aidanmontag13/MultiPlaneDisplay/3Dmodels/tex_u0_v0_diffuse.jpg

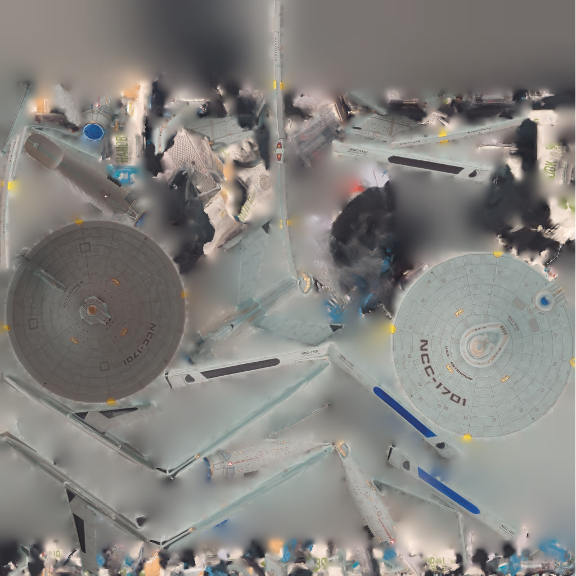
3Dmodels/tex_u0_v0_diffuse.jpg
