aidanmontag13/MultiPlaneDisplay/6.jpg

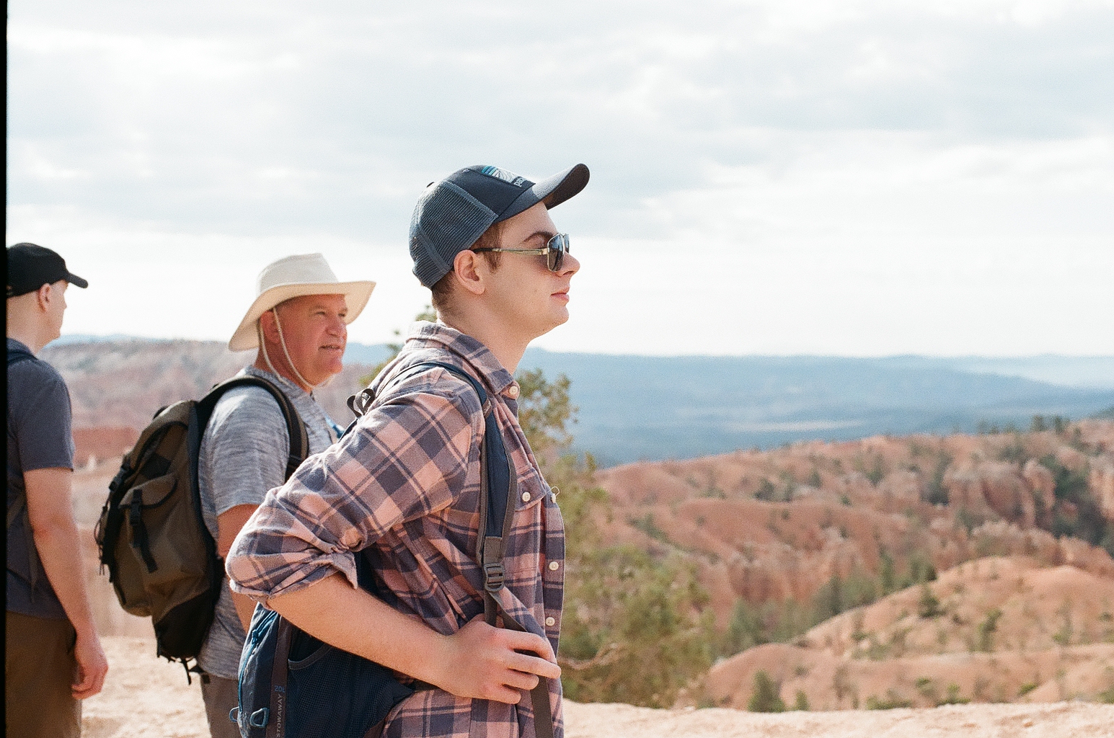
6.jpg
