aidanmontag13/MultiPlaneDisplay/artifacts/Diagram2.png

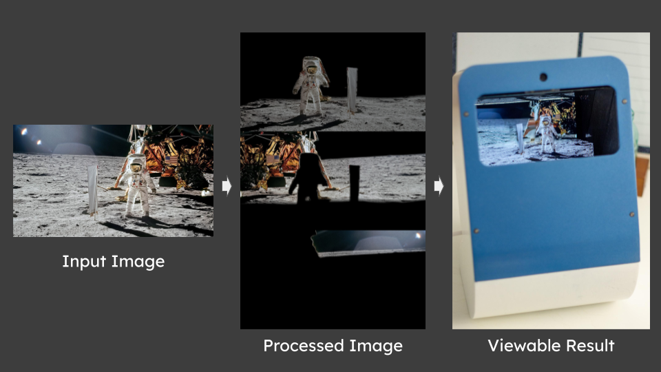
artifacts/Diagram2.png
