aidanmontag13/MultiPlaneDisplay/artifacts/Render.png

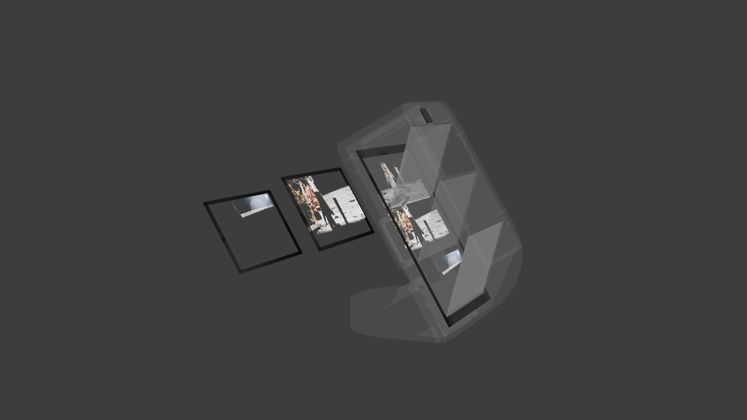
artifacts/Render.png
