aidanmontag13/MultiPlaneDisplay/multiplane_headtracker.py

from math import sqrt
import onnxruntime as ort
import cv2
import numpy as np
import glob
import os
import time
import copy
import open3d as o3d
from skimage.filters import threshold_multiotsu

import headtracker
import queue
import threading
from ultralytics import YOLO

H = 213
W = 400
PROJECTION_DISTANCE = 0.3
SCREEN_0_DISTANCE = 0.0
SCREEN_1_DISTANCE = 0.07239
SCREEN_2_DISTANCE = 0.1452
DEPTH_RANGE = 0.21718
DISPLAY_WIDTH = 0.13596

# Load model
session = ort.InferenceSession(
    "models/depth_anything/depth_anything_v2_vits.onnx",
    providers=['CPUExecutionProvider']
)

# Get correct input name
input_name = session.get_inputs()[0].name

def find_usb_images():
    user = "multiplane"
    media_root = f"/media/{user}"

    image_paths = []

    # Loop over all USB drives
    for drive in os.listdir(media_root):
        drive_path = os.path.join(media_root, drive)
        images_folder = os.path.join(drive_path, "images")
        output_folder = os.path.join(drive_path, "display")

        if os.path.isdir(images_folder):
            print(f"Found images folder on USB: {images_folder}")

            # Add all image files (jpg, png, tiff)
            for ext in ("*.jpg", "*.jpeg", "*.png", "*.tif", "*.tiff"):
                image_paths.extend(glob.glob(os.path.join(images_folder, ext)))
        else:
            print(f"No images folder found on USB: {drive_path}")
            continue

    return image_paths, output_folder

def resize_and_crop(img, target_size):
    target_w, target_h = target_size
    h, w = img.shape[:2]
    
    # Compute scale factor to cover the target
    scale = target_w / w
    
    # Resize image
    new_w = int(w * scale)
    new_h = int(h * scale)
    #print(f"Resizing from ({w}, {h}) to ({new_w}, {new_h})")
    if w / h > target_w / target_h:
        resized = cv2.resize(img, (new_w, target_h), interpolation=cv2.INTER_LINEAR)
        start_x = (new_w - target_w) // 2
        cropped = resized[:, start_x:start_x + target_w]
    else:
        resized = cv2.resize(img, (target_w, new_h), interpolation=cv2.INTER_LINEAR)
        start_y = (new_h - target_h) // 2
        cropped = resized[start_y:start_y + target_h, :]
    
    return cropped

def preprocess(image):
    img = cv2.cvtColor(image, cv2.COLOR_BGR2RGB)
    img = cv2.resize(img, (518, 518))
    img = img.astype(np.float32) / 255.0

    # model normalization
    mean = np.array([0.5, 0.5, 0.5], dtype=np.float32)
    std  = np.array([0.5, 0.5, 0.5], dtype=np.float32)
    img = (img - mean) / std

    img = img.transpose(2, 0, 1)  # HWC → CHW
    img = img[None, ...]          # add batch dim
    return img

def infer(inp):
    out = session.run(None, {input_name: inp})
    depth = out[0][0]

    # rescale depth for saving
    depth = (depth - depth.min()) / (depth.max() - depth.min())
    return depth

def create_pointcloud(color, depth):

    depth = depth * DEPTH_RANGE + (PROJECTION_DISTANCE - DEPTH_RANGE / 6)

    h, w = color.shape[:2]
    depth = cv2.resize(depth, (w, h), interpolation=cv2.INTER_LINEAR)

    fx = (w / DISPLAY_WIDTH) * PROJECTION_DISTANCE
    fy = fx
    cx = W / 2
    cy = H / 2

    color_o3d = o3d.geometry.Image((color).astype(np.uint8))
    depth_o3d = o3d.geometry.Image((depth * (1000)).astype(np.uint16))

    rgbd_image = o3d.geometry.RGBDImage.create_from_color_and_depth(
        color_o3d, depth_o3d, convert_rgb_to_intensity=False
    )

    intrinsics = o3d.camera.PinholeCameraIntrinsic(w, h, fx, fy, cx, cy)
    pcd = o3d.geometry.PointCloud.create_from_rgbd_image(rgbd_image, intrinsics)
    pcd, ind = pcd.remove_statistical_outlier(nb_neighbors=20, std_ratio=2.0)

    origin = o3d.geometry.TriangleMesh.create_coordinate_frame(size=0.01)

    o3d.visualization.draw_geometries([pcd, origin])

    return pcd

def despeckle(mask, kernel_size):
    kernel = np.ones((kernel_size,kernel_size), np.uint8)   # or (5,5) depending on outline thickness
    mask = mask * -1 + 1
    mask = (mask * 255).astype(np.uint8)
    closed = cv2.morphologyEx(mask, cv2.MORPH_CLOSE, kernel)
    mask = (closed.astype(np.float32)) / 255.0
    mask = mask * -1 + 1
    return mask

def blur_and_dilate(mask, blur_size):
    mask = mask * -1 + 1
    kernel = np.ones((int(blur_size * 0.3), int(blur_size * 0.3)), np.uint8)
    mask_uint8 = (mask * 255).astype(np.uint8)
    expanded = cv2.dilate(mask_uint8, kernel)
    mask = expanded.astype(np.float32) / 255.0
    mask = mask * -1 + 1
    mask = cv2.GaussianBlur(mask, (blur_size, blur_size), 0)
    return mask

def create_mask(depth, low_thresh, high_thresh, rolloff_a, rolloff_b, blur):
    mask = np.zeros_like(depth, dtype=np.float32)

    if rolloff_a == 0 and rolloff_b == 0:
        mask = ((depth >= low_thresh) & (depth <= high_thresh)).astype(np.float32)
        mask = blur_and_dilate(mask, blur)
        mask = despeckle(mask, kernel_size=3)
        mask = cv2.resize(mask, (W, H), interpolation=cv2.INTER_LINEAR)
        return mask
    
    lower_ramp = (depth - (low_thresh - 0.5 * rolloff_a)) / rolloff_a
    lower_ramp = np.clip(lower_ramp, 0, 1)
    
    upper_ramp = ((high_thresh + 0.5 * rolloff_b) - depth) / rolloff_b
    upper_ramp = np.clip(upper_ramp, 0, 1)
    
    if low_thresh == 0:
        mask = upper_ramp
    elif high_thresh == 1:
        mask = lower_ramp
    else:
        mask = np.minimum(lower_ramp, upper_ramp)

    mask = despeckle(mask, kernel_size=3)
    mask = blur_and_dilate(mask, blur)

    mask = cv2.resize(mask, (W, H), interpolation=cv2.INTER_LINEAR)
    
    return mask

def apply_mask(image, mask):
    mask = np.repeat(mask[:, :, np.newaxis], 3, axis=2)
    masked_image = image * mask
    return masked_image

def inpaint_mask(image, mask):
    mask = 1.0 - mask
    mask = cv2.resize(mask, (W, H), interpolation=cv2.INTER_LINEAR)
    mask_uint8 = (mask * 255).astype(np.uint8)
    kernel = np.ones((int(3), int(3)), np.uint8)
    mask = cv2.dilate(mask_uint8, kernel)
    inpainted = cv2.inpaint((image * 255).astype(np.uint8), mask_uint8, 5, cv2.INPAINT_NS)
    inpainted = inpainted.astype(np.float32) / 255.0
    return inpainted

def render_perspective(point_cloud, viewer_position, inpaint=True):
    pcd = copy.deepcopy(point_cloud)
    fx = (W / DISPLAY_WIDTH) * PROJECTION_DISTANCE
    fy = fx
    cx = W / 2
    cy = H / 2

    # move point cloud to center
    translation = np.array([0, 0, -PROJECTION_DISTANCE])
    pcd.translate(translation, relative=True)

    # calculate pitch and yaw angle to keep camera centered
    yaw_angle = np.arctan((viewer_position[0]) / viewer_position[1])
    pitch_angle = np.arctan((viewer_position[2]) / viewer_position[1])

    # rotate object
    rotation_matrix = pcd.get_rotation_matrix_from_xyz((pitch_angle, yaw_angle, 0))
    pcd.rotate(rotation_matrix, center=(0, 0, 0))

    # find offset
    viewer_distance = np.linalg.norm(viewer_position)
    offset_translation = np.array([0, 0, viewer_distance])
    pcd.translate(offset_translation, relative=True)

    #origin = o3d.geometry.TriangleMesh.create_coordinate_frame(size=0.1)

    #o3d.visualization.draw_geometries([pcd, pcd_og, origin])

    # Project point cloud back to image plane
    points = np.asarray(pcd.points)
    colors = np.asarray(pcd.colors)
    
    # Project 3D points to 2D
    x_proj = (points[:, 0] * fx / points[:, 2]) + cx
    y_proj = (points[:, 1] * fy / points[:, 2]) + cy
    
    # Create output image and depth buffer
    warped = np.zeros((H, W, 3), dtype=np.float32)
    depth_buffer = np.full((H, W), np.inf, dtype=np.float32)
    
    # Render points to image, keeping closest point
    valid_mask = (points[:, 2] > 0) & \
                 (x_proj >= 0) & (x_proj < W) & \
                 (y_proj >= 0) & (y_proj < H)
    
    x_proj = x_proj[valid_mask].astype(np.int32)
    y_proj = y_proj[valid_mask].astype(np.int32)
    z_depth = points[valid_mask, 2]
    colors_valid = colors[valid_mask]
    
    for i in range(len(x_proj)):
        # Only update if this point is closer than what's already there
        if z_depth[i] < depth_buffer[y_proj[i], x_proj[i]]:
            warped[y_proj[i], x_proj[i]] = colors_valid[i]
            depth_buffer[y_proj[i], x_proj[i]] = z_depth[i]

    mask = (depth_buffer == np.inf).astype(np.uint8)
    mask = 1 - mask
    
    if inpaint == True:
        warped = inpaint_mask(warped, mask)
        depth_buffer = inpaint_mask(depth_buffer, mask)
    
    return warped, depth_buffer, viewer_distance

def legacy_render_perspective(point_cloud, viewer_position, inpaint=True):
    
    pcd = copy.deepcopy(point_cloud)
    fx = (W / DISPLAY_WIDTH) * PROJECTION_DISTANCE
    fy = fx
    cx = W / 2
    cy = H / 2

    # move point cloud to center
    translation = np.array([0, 0, -PROJECTION_DISTANCE])
    pcd.translate(translation, relative=True)

    # calculate pitch and yaw angle to keep camera centered
    yaw_angle = np.arctan((viewer_position[0]) / viewer_position[1])
    pitch_angle = np.arctan((viewer_position[2]) / viewer_position[1])

    # rotate object
    rotation_matrix = pcd.get_rotation_matrix_from_xyz((pitch_angle, yaw_angle, 0))
    pcd.rotate(rotation_matrix, center=(0, 0, 0))

    # find offset
    viewer_distance = np.linalg.norm(viewer_position)
    offset_translation = np.array([0, 0, viewer_distance])
    pcd.translate(offset_translation, relative=True)

    vis = o3d.visualization.Visualizer()
    vis.create_window(visible=False, width=W, height=H)

    w_act = vis.get_render_option().mesh_show_back_face  # fake call just to init controller
    ctr = vis.get_view_control()

    params_now = ctr.convert_to_pinhole_camera_parameters()
    print("Window intrinsic size actually used by Open3D:", 
      params_now.intrinsic.width, params_now.intrinsic.height)

    vis.add_geometry(pcd)

    intrinsic = o3d.camera.PinholeCameraIntrinsic()
    intrinsic.set_intrinsics(W, H, fx, fy, cx, cy)

    extrinsic = np.eye(4) 

    cam_params = o3d.camera.PinholeCameraParameters()
    cam_params.intrinsic = intrinsic
    print("intrinsic", cam_params.intrinsic)
    cam_params.extrinsic = extrinsic

    ctr = vis.get_view_control()
    ctr.convert_from_pinhole_camera_parameters(cam_params)

    vis.poll_events()
    vis.update_renderer()

    color_o3d = vis.capture_screen_float_buffer(do_render=True)
    depth_o3d = vis.capture_depth_float_buffer(do_render=True)

    vis.destroy_window()

    color = np.asarray(color_o3d, dtype=np.float32)
    depth = np.asarray(depth_o3d, dtype=np.float32)

    if inpaint:
        mask = (depth > 0).astype(np.uint8)
        color = inpaint_mask(color, mask)
        depth = inpaint_mask(depth, mask)

    return color, depth, viewer_distance

def new_render_perspective(point_cloud, viewer_position, inpaint=True):
    pcd = copy.deepcopy(point_cloud)

    fx = (W / DISPLAY_WIDTH) * PROJECTION_DISTANCE
    fy = fx
    cx = W / 2
    cy = H / 2

    # move point cloud to center
    translation = np.array([0, 0, -PROJECTION_DISTANCE])
    pcd.translate(translation, relative=True)

    # your yaw/pitch system
    yaw_angle   = np.arctan((viewer_position[0]) / viewer_position[1])
    pitch_angle = np.arctan((viewer_position[2]) / viewer_position[1])

    rotation_matrix = pcd.get_rotation_matrix_from_xyz((pitch_angle, yaw_angle, 0))
    pcd.rotate(rotation_matrix, center=(0, 0, 0))

    # your offset
    viewer_distance = np.linalg.norm(viewer_position)
    offset_translation = np.array([0, 0, viewer_distance])
    pcd.translate(offset_translation, relative=True)

    renderer = o3d.visualization.rendering.OffscreenRenderer(W, H)
    scene = renderer.scene
    scene.set_background([0, 0, 0, 0])

    # add geometry
    material = o3d.visualization.rendering.MaterialRecord()
    material.shader = "defaultUnlit"
    material.point_size = 2.0
    scene.add_geometry("pcd", pcd, material)

    K = np.array([
        [fx, 0,  cx],
        [0,  fy, cy],
        [0,  0,   1]
    ], dtype=np.float64)

    # extrinsic is identity, because you ALREADY moved + rotated the point cloud
    extrinsic = np.eye(4)

    renderer.setup_camera(
        intrinsic_matrix=K,
        extrinsic_matrix=extrinsic,
        intrinsic_width_px=W,
        intrinsic_height_px=H
    )

    color_o3d = renderer.render_to_image()
    depth_o3d = renderer.render_to_depth_image(z_in_view_space=True)

    color = (np.asarray(color_o3d).astype(np.float32) / 255.0)
    depth = np.asarray(depth_o3d).astype(np.float32)

    if inpaint:
        mask = (depth > 0).astype(np.uint8)
        color = inpaint_mask(color, mask)
        depth = inpaint_mask(depth, mask)

    return color, depth

def reproject_2D(color, viewer_position, plane_depth):
    h, w = color.shape[:2]
    fx = (w / DISPLAY_WIDTH) * PROJECTION_DISTANCE
    fy = fx
    cx = W / 2
    cy = H / 2
    
    K = np.array([
        [fx, 0, cx],
        [0, fy, cy],
        [0, 0, 1]
    ])
    
    src_points = np.float32([
        [0, 0],           # Top-left
        [W, 0],           # Top-right
        [W, H],           # Bottom-right
        [0, H]            # Bottom-left
    ])

    pts_h = np.hstack([src_points, np.ones((src_points.shape[0], 1))])

    K_inv = np.linalg.inv(K)

    pts_3d = (K_inv @ pts_h.T).T

    #print("3d points", pts_3d)

    # create point cloud
    pcd = o3d.geometry.PointCloud()
    pcd.points = o3d.utility.Vector3dVector(pts_3d)
    pcd_og = o3d.geometry.PointCloud()
    pcd_og.points = o3d.utility.Vector3dVector(pts_3d)
    origin = o3d.geometry.TriangleMesh.create_coordinate_frame()

    # Project corner points
    offset_depth = 1 - (plane_depth / PROJECTION_DISTANCE)
    #print("offset depth", offset_depth)
    t1 = np.array([0, 0, -offset_depth])
    pcd.translate(t1, relative=True)
    
    yaw_angle = np.arctan2(viewer_position[0], viewer_position[1])
    pitch_angle = np.arctan2(viewer_position[2], viewer_position[1])

    rotation_matrix = pcd.get_rotation_matrix_from_xyz((pitch_angle, yaw_angle, 0))
    pcd.rotate(rotation_matrix, center=(0, 0, 0))

    # find offset
    offset_distance = np.linalg.norm(viewer_position) / PROJECTION_DISTANCE
    offset_translation = np.array([0, 0, offset_distance])
    pcd.translate(offset_translation, relative=True)

    #o3d.visualization.draw_geometries([pcd, pcd_og])
    
    transformed = np.asarray(pcd.points)  # (4×3)

    # Reproject to 2D
    proj = (K @ transformed.T).T
    dst_pts = proj[:, :2] / proj[:, 2:3]     # normalize by Z
    
    # Apply 2D warp
    H_mat = cv2.getPerspectiveTransform(src_points, dst_pts.astype(np.float32))
    H_inv = np.linalg.inv(H_mat)
    warped = cv2.warpPerspective(color, H_inv, (W, H))
    
    return warped
    
def stack_images(foreground, middleground, background):
    foreground_flipped = cv2.flip(foreground, 0) * (0.33, 0.33, 0.33)
    middleground_flipped = cv2.flip(middleground, 0) * (0.8, 0.9, 1.0)
    background_flipped = cv2.flip(background, 0) * (2.8, 3.15, 3.5)
    #combined = np.vstack((background_flipped, middleground_flipped, foreground_flipped))
    combined = np.vstack((foreground, middleground, background))

    combined = np.clip(combined, 0, 1)
    combined_srgb = (combined ** (1/2.2) * 255.0).astype(np.uint8)
    combined_srgb = cv2.resize(combined_srgb, (800, 1280), interpolation=cv2.INTER_LINEAR)
    return combined_srgb

def prepare_plane(image, depth, viewer_position, plane_depth, t1, t2, rolloff_a, rolloff_b, blur):
    linear_perspective_image = (image.astype(np.float32)) ** 2.2
    mask = create_mask(depth, t1, t2, rolloff_a, rolloff_b, blur)
    masked_image = apply_mask(linear_perspective_image, mask)
    warped_image = reproject_2D(masked_image, viewer_position, plane_depth)

    return warped_image

def initialize_render(image_path):
    image = cv2.imread(image_path)
    image = resize_and_crop(image, (W, H))
    inp = preprocess(image)
    depth = infer(inp)
    depth = 1 - depth
    depth = depth ** (2.2)
    ot1, ot2 = threshold_multiotsu(depth, classes=3)

    pcd = create_pointcloud(image, depth)

    return pcd, ot1, ot2

def renderer_worker(pcd, ot1, ot2, rolloff_a, rolloff_b, position_queue, stop_event, inpaint=False):
    while not stop_event.is_set():
        print("position_queue", position_queue)
        position = position_queue.get()

        x, y, z = position
        print("got position", x, y, z)
        

        render, depth, viewer_distance = render_perspective(pcd, [x, y, z], inpaint)

        t1 = viewer_distance + DEPTH_RANGE * 0.33
        t2 = viewer_distance + DEPTH_RANGE * 0.66
        #t1 = viewer_distance + DEPTH_RANGE * ot1
        #t2 = viewer_distance + DEPTH_RANGE * ot2
        t3 = 100

        foreground = prepare_plane(render, depth, [x, y, z], SCREEN_0_DISTANCE, 0, t1, 0, rolloff_a, 3)
        middleground = prepare_plane(render, depth, [x, y, z], SCREEN_1_DISTANCE, t1, t2, rolloff_a, rolloff_b, 3)
        background = prepare_plane(render, depth, [x, y, z], SCREEN_2_DISTANCE, t2, t3, rolloff_b, 0, 3)

        combined_image = stack_images(foreground, middleground, background) 

        #cv2.namedWindow("combined_image", cv2.WINDOW_NORMAL)
        #cv2.setWindowProperty("combined_image", cv2.WND_PROP_FULLSCREEN, cv2.WINDOW_FULLSCREEN)
        cv2.imshow("combined_image", combined_image)
        position_queue.task_done()
        if cv2.waitKey(1) & 0xFF == ord('q'):
            break

def main():
    image_path = "images/lunch.jpg"

    cap, model, camera_matrix, dist_coeffs = headtracker.initialize_headtracker()
    position_queue = queue.Queue(maxsize=1)
    stop_event = threading.Event()
    
    headtracker_thread = threading.Thread(
        target=headtracker.headtracker_worker,
        args=(cap, model, camera_matrix, dist_coeffs, position_queue, stop_event),
        daemon=False,
    )

    pcd, ot1, ot2 = initialize_render(image_path)

    rolloff_a = SCREEN_1_DISTANCE * 1
    rolloff_b = SCREEN_1_DISTANCE * 1

    renderer_thread = threading.Thread(
        target=renderer_worker,
        args=(pcd, ot1, ot2, rolloff_a, rolloff_b, position_queue, stop_event),
        daemon=False,
    )

    headtracker_thread.start()
    renderer_thread.start()

    time.sleep(30)
    stop_event.set()
    headtracker_thread.join()
    renderer_thread.join()

if __name__ == "__main__":
    main()
